Kayto/AT65C02/Images/20230501_125532.jpg

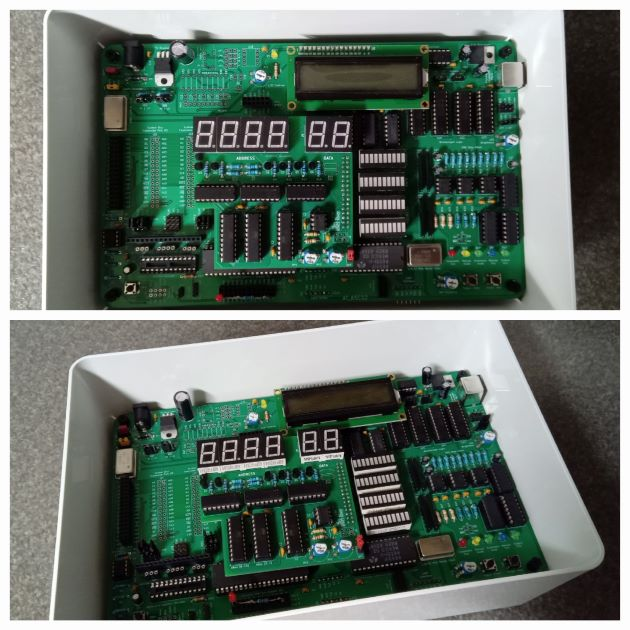
Images/20230501_125532.jpg
