Kayto/AT65C02/KiCad/Hex Display Rev003/AT65C02_HEX_rev003.jpg

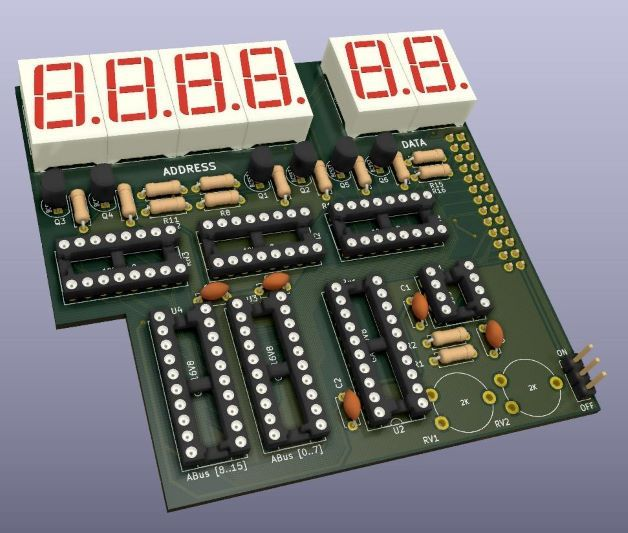
KiCad/Hex Display Rev003/AT65C02_HEX_rev003.jpg
