Kayto/AT65C02/KiCad/Hex Display Rev003/AT65C02_HEX_rev003_FRONT.jpg

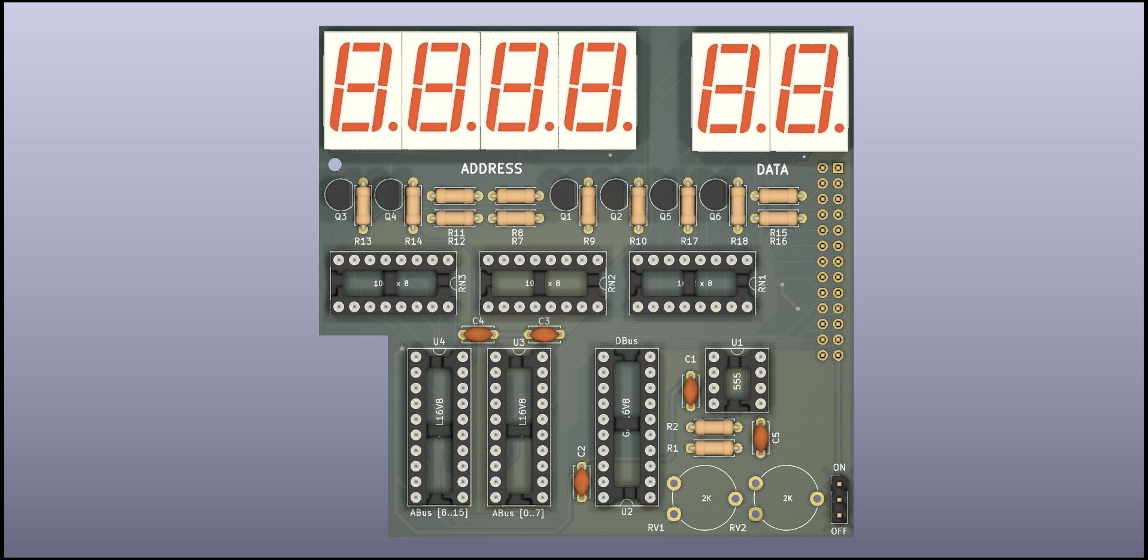
KiCad/Hex Display Rev003/AT65C02_HEX_rev003_FRONT.jpg
