Kayto/AT65C02/KiCad/Memory Decoder/Memory Decoder_back.jpg

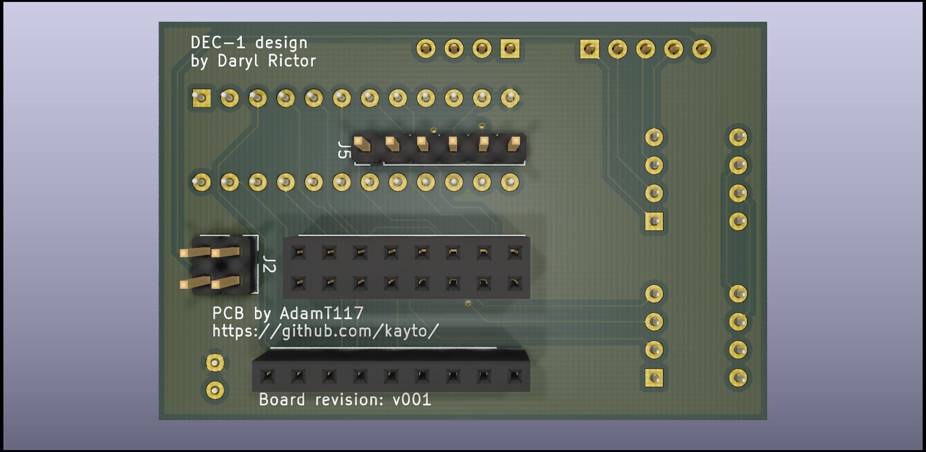
KiCad/Memory Decoder/Memory Decoder_back.jpg
