Kayto/AT65C02/KiCad/Memory Decoder/Memory Decoder_pcb_front.jpg

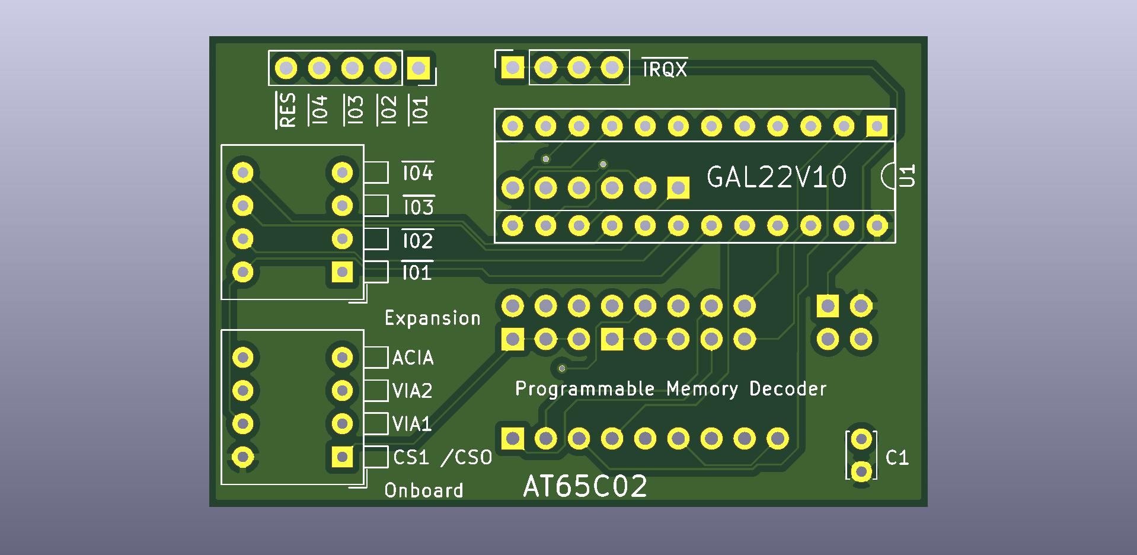
KiCad/Memory Decoder/Memory Decoder_pcb_front.jpg
