Kayto/AT65C02/Software/Software _ATOS/BASIC/fib.bas

10 REM Fibonacci Sequence Generator
20 PRINT "FIBONACCI SEQUENCE"
30 PRINT
40 PRINT "HOW MANY NUMBERS";
50 INPUT N
60 IF N < 1 THEN GOTO 40
70 PRINT
80 A = 0
90 B = 1
100 PRINT "1: "; A
110 PRINT "2: "; B
120 FOR I = 3 TO N
130 C = A + B
140 PRINT I; ": "; C
150 A = B
160 B = C
170 NEXT I
180 END
