Kayto/AT65C02/Software/Software _ATOS/BASIC/input.bas

10 REM String and Input Test
20 PRINT "STRING AND INPUT TEST"
30 PRINT
40 PRINT "WHAT IS YOUR NAME";
50 INPUT N$
60 PRINT
70 PRINT "HELLO, "; N$; "!"
80 PRINT
90 PRINT "HOW OLD ARE YOU";
100 INPUT A
110 PRINT
120 PRINT "IN 10 YEARS YOU WILL BE "; A+10
130 PRINT
140 PRINT "NICE TO MEET YOU, "; N$
150 END
