Kayto/AT65C02/Software/Software _ATOS/BASIC/lcdclear.bas

10 REM LCD CLEAR TEST
20 PRINT "LCD CLEAR"
30 MC = 30000
40 REM LOAD LCD CLEAR CODE
50 FOR I = 0 TO 41
60 READ B
70 POKE MC + I, B
80 NEXT I
90 PRINT "CLEARING LCD"
100 POKE 10, 76
110 POKE 11, MC AND 255
120 POKE 12, MC / 256
130 X = USR(0)
140 PRINT "DONE"
150 END
1000 REM LCD CLEAR 0x01
1010 REM HIGH NIBBLE 0 RS=0
1020 DATA 169,0,141,0,144
1030 REM E HIGH
1040 DATA 169,8,141,0,144
1050 REM SHORT DELAY
1060 DATA 234,234,234
1070 REM E LOW
1080 DATA 169,0,141,0,144
1090 REM LOW NIBBLE 1 RS=0
1100 DATA 169,16,141,0,144
1110 REM E HIGH
1120 DATA 169,24,141,0,144
1130 REM SHORT DELAY
1140 DATA 234,234,234
1150 REM E LOW
1160 DATA 169,16,141,0,144
1170 REM SHORT DELAY
1180 DATA 162,50,202,208,253
1190 DATA 96
