Kayto/AT65C02/Software/Software _ATOS/BASIC/ledblink.bas

10 REM LED BLINK CONTROL
20 PRINT "LED CONTROLLER"
30 PRINT
40 REM VIA ADDRESSES
50 VB = 36864: REM VIA DRB
55 DD = 36866: REM VIA DDRB
56 REM SET BIT 0 AS OUTPUT
57 V = PEEK(DD)
58 V = V OR 1
59 POKE DD, V
60 PRINT "COMMANDS:"
70 PRINT "1 - LED ON"
80 PRINT "2 - LED OFF"
90 PRINT "3 - SLOW BLINK"
100 PRINT "4 - FAST BLINK"
110 PRINT "5 - SOS PATTERN"
120 PRINT "6 - CUSTOM RATE"
130 PRINT "0 - EXIT"
140 PRINT
150 INPUT "CHOICE"; C
160 IF C = 0 THEN END
170 IF C = 1 THEN GOSUB 1000
180 IF C = 2 THEN GOSUB 1100
190 IF C = 3 THEN GOSUB 1200
200 IF C = 4 THEN GOSUB 1300
210 IF C = 5 THEN GOSUB 1400
220 IF C = 6 THEN GOSUB 1700
230 GOTO 140
1000 REM LED ON
1010 PRINT "LED ON"
1020 V = PEEK(VB)
1030 V = V OR 1
1040 POKE VB, V
1050 RETURN
1100 REM LED OFF
1110 PRINT "LED OFF"
1120 V = PEEK(VB)
1130 V = V AND 254
1140 POKE VB, V
1150 RETURN
1200 REM SLOW BLINK
1210 PRINT "SLOW BLINK (10 TIMES)"
1220 FOR N = 1 TO 10
1230 GOSUB 1000
1240 FOR I = 1 TO 500: NEXT I
1250 GOSUB 1100
1260 FOR I = 1 TO 500: NEXT I
1270 NEXT N
1280 RETURN
1300 REM FAST BLINK
1310 PRINT "FAST BLINK (20 TIMES)"
1320 FOR N = 1 TO 20
1330 GOSUB 1000
1340 FOR I = 1 TO 50: NEXT I
1350 GOSUB 1100
1360 FOR I = 1 TO 50: NEXT I
1370 NEXT N
1380 RETURN
1400 REM SOS PATTERN
1410 PRINT "SOS PATTERN"
1420 REM THREE SHORT
1430 FOR J = 1 TO 3
1440 GOSUB 1000
1450 FOR I = 1 TO 100: NEXT I
1460 GOSUB 1100
1470 FOR I = 1 TO 100: NEXT I
1480 NEXT J
1490 REM THREE LONG
1500 FOR J = 1 TO 3
1510 GOSUB 1000
1520 FOR I = 1 TO 300: NEXT I
1530 GOSUB 1100
1540 FOR I = 1 TO 100: NEXT I
1550 NEXT J
1560 REM THREE SHORT
1570 FOR J = 1 TO 3
1580 GOSUB 1000
1590 FOR I = 1 TO 100: NEXT I
1595 GOSUB 1100
1596 FOR I = 1 TO 100: NEXT I
1597 NEXT J
1598 FOR I = 1 TO 1000: NEXT I
1599 RETURN
1700 REM CUSTOM RATE
1710 INPUT "DELAY (1-1000)"; D
1720 INPUT "HOW MANY TIMES"; T
1730 PRINT "CUSTOM BLINK"
1740 FOR N = 1 TO T
1750 GOSUB 1000
1760 FOR I = 1 TO D: NEXT I
1770 GOSUB 1100
1780 FOR I = 1 TO D: NEXT I
1790 NEXT N
1800 RETURN
