Kayto/AT65C02/Software/Software _ATOS/BASIC/memtest.bas

10 REM Memory Test - Shows Available RAM
20 PRINT "EHBASIC MEMORY TEST"
30 PRINT
40 PRINT "FREE MEMORY: "; FRE(0); " BYTES"
50 PRINT
60 REM Allocate some arrays
70 DIM A(100)
80 DIM B$(10)
90 PRINT "AFTER ALLOCATING ARRAYS:"
100 PRINT "FREE MEMORY: "; FRE(0); " BYTES"
110 PRINT
120 REM Fill array with values
130 FOR I = 1 TO 100
140 A(I) = I * 2
150 NEXT I
160 PRINT "ARRAY A(1-10):"
170 FOR I = 1 TO 10
180 PRINT A(I);
190 NEXT I
200 PRINT
210 END
