Kayto/AT65C02/Software/Software _ATOS/BASIC/mltest.bas

10 REM ML SYNTAX TEST
20 PRINT "TESTING ML SYNTAX"
30 PRINT
40 REM USE HIGH RAM FOR ML
50 MC = 30000
60 POKE 10, 76
70 POKE 11, MC AND 255
80 POKE 12, MC / 256
90 REM CREATE TEST CODE
100 POKE MC, 169
110 POKE MC + 1, 42
120 POKE MC + 2, 96
130 PRINT "CALLING ML CODE"
140 X = USR(0)
150 PRINT "RETURNED"
160 PRINT X
170 END
