Kayto/AT65C02/Software/Software _ATOS/BASIC/usrtest.bas

10 REM TEST USR MULTIPLE CALLS
20 PRINT "USR TEST"
30 MC = 30000
40 REM SIMPLE CODE LDA 65 RTS
50 POKE MC, 165
60 POKE MC + 1, 101
70 POKE MC + 2, 96
80 PRINT "CALLING 3 TIMES"
90 FOR I = 1 TO 3
100 POKE 101, I
110 GOSUB 1000
120 PRINT "CALL"; I; "OK"
130 NEXT I
140 PRINT "DONE"
150 END
1000 REM USR CALL
1010 POKE 10, 76
1020 POKE 11, MC AND 255
1030 POKE 12, MC / 256
1040 X = USR(0)
1050 RETURN
